danyv86/ME-1670---SOLIDWORKS-Functional-Design-Team-Project/Daniel Velazquez TOOLIO Drawings/BOLT DRAWING.PNG

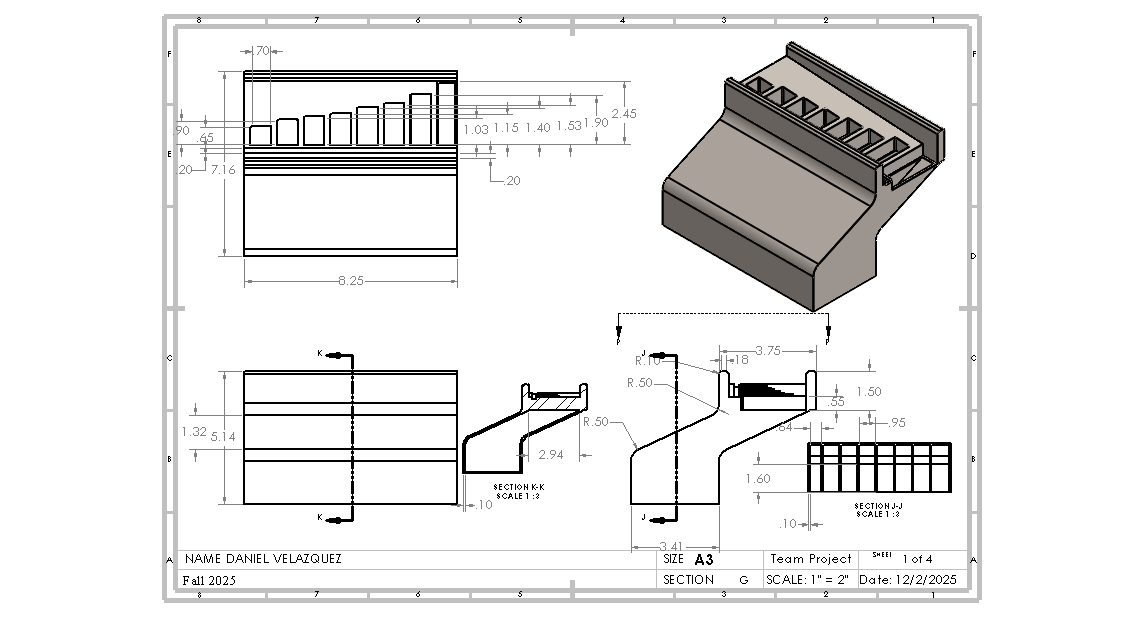
Daniel Velazquez TOOLIO Drawings/BOLT DRAWING.PNG
