danyv86/ME-1670---SOLIDWORKS-Functional-Design-Team-Project/Daniel Velazquez TOOLIO Drawings/REAL FINAL SUBASSEMLY DRAWINF.PNG

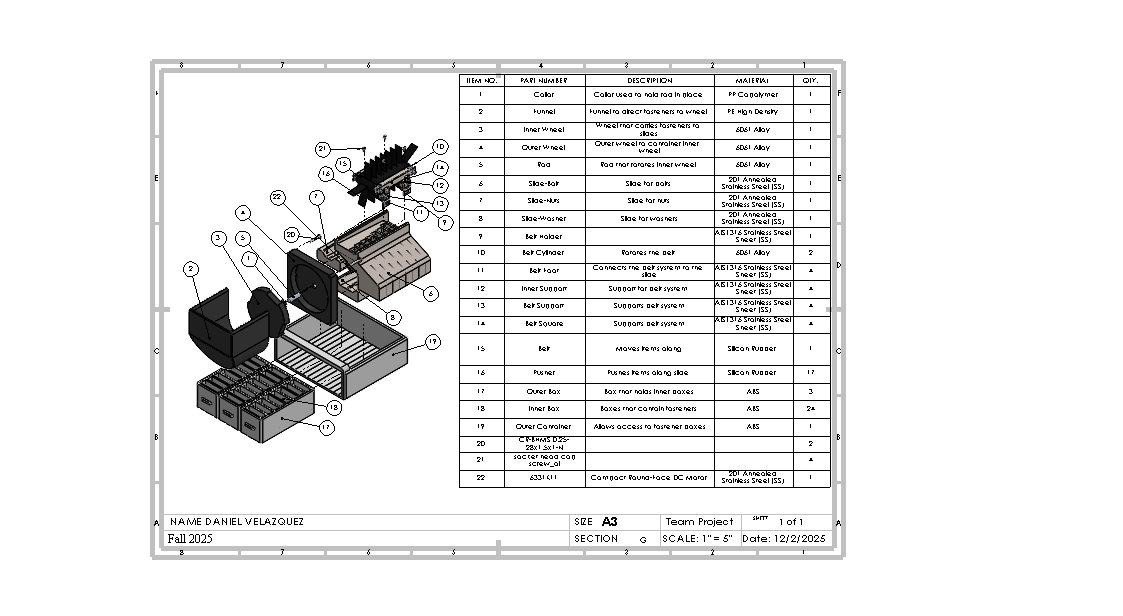
Daniel Velazquez TOOLIO Drawings/REAL FINAL SUBASSEMLY DRAWINF.PNG
