danyv86/ME-1670---SOLIDWORKS-Functional-Design-Team-Project/Daniel Velazquez TOOLIO Part PNGs/11.PNG

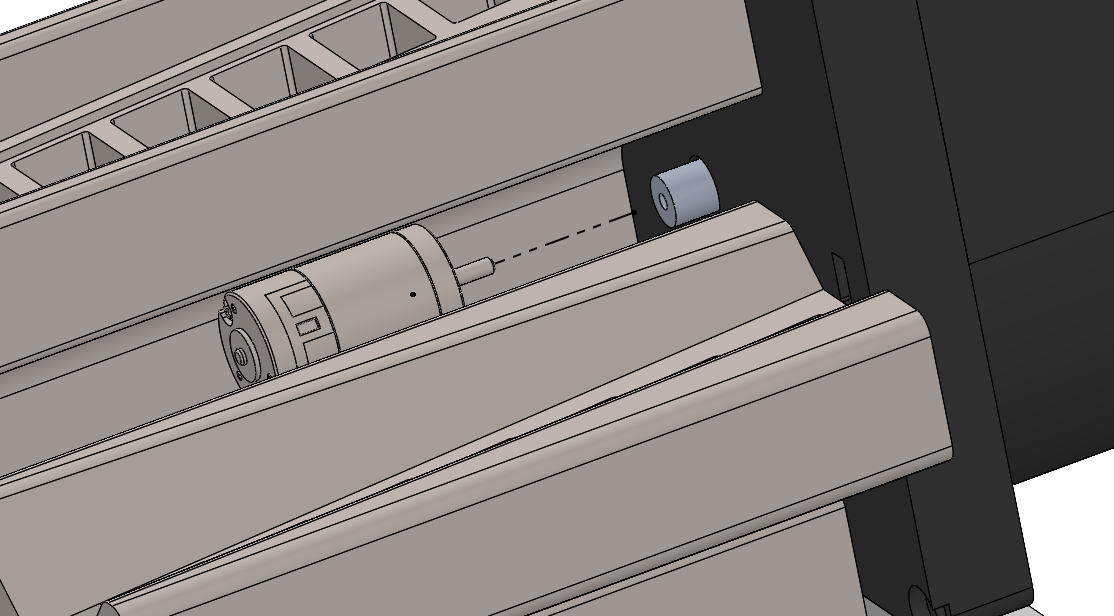
Daniel Velazquez TOOLIO Part PNGs/11.PNG
