danyv86/ME-1670---SOLIDWORKS-Functional-Design-Team-Project/Daniel Velazquez TOOLIO Part PNGs/al.PNG

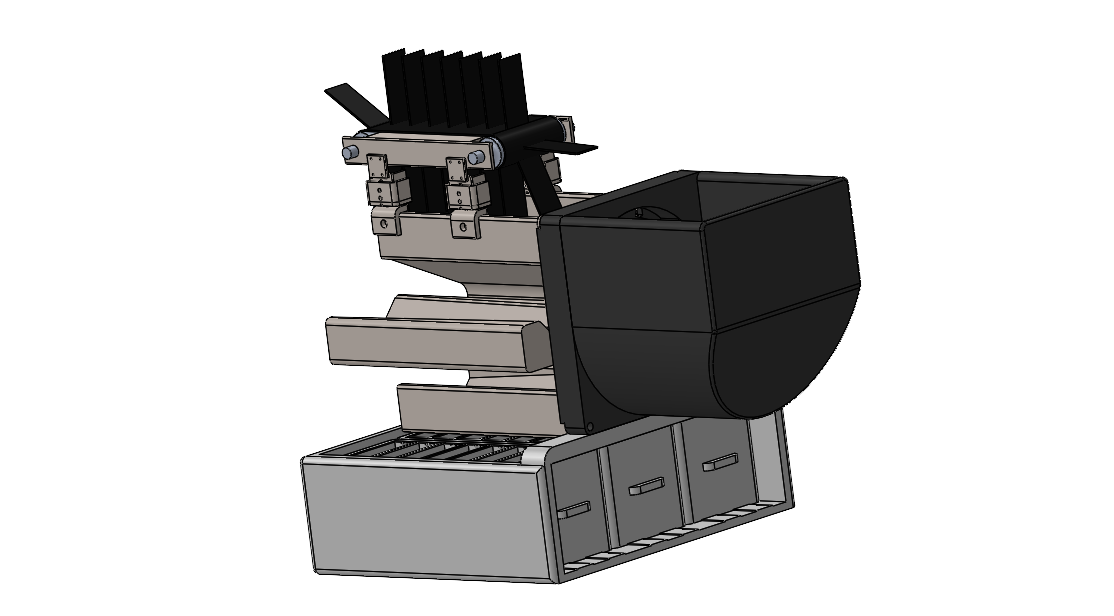
Daniel Velazquez TOOLIO Part PNGs/al.PNG
