danyv86/ME-1670---SOLIDWORKS-Functional-Design-Team-Project/Daniel Velazquez TOOLIO Part PNGs/Velazquez_Daniel_angle_bracket.PNG

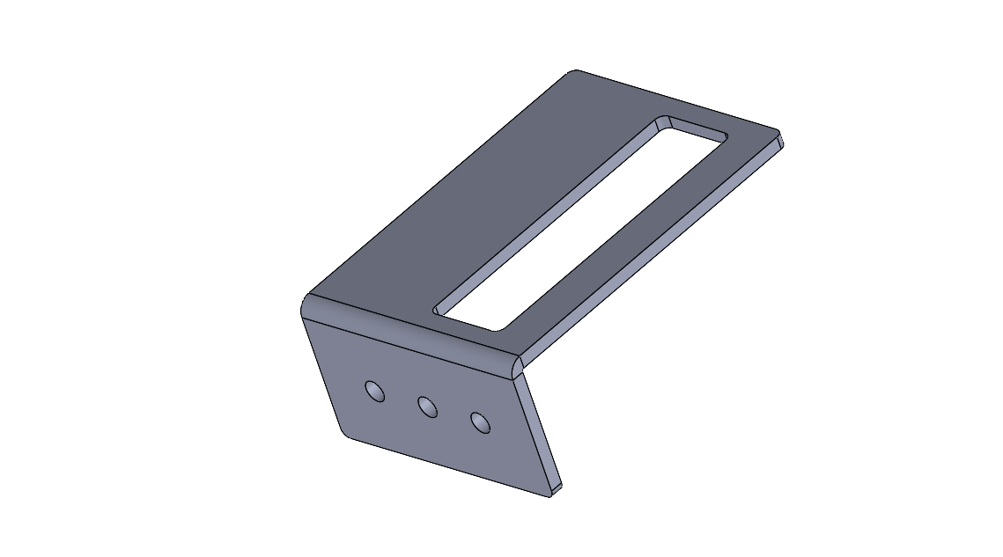
Daniel Velazquez TOOLIO Part PNGs/Velazquez_Daniel_angle_bracket.PNG
