danyv86/ME-1670---SOLIDWORKS-Functional-Design-Team-Project/Daniel Velazquez TOOLIO Part PNGs/Velazquez_Daniel_team_inner_wheel.PNG

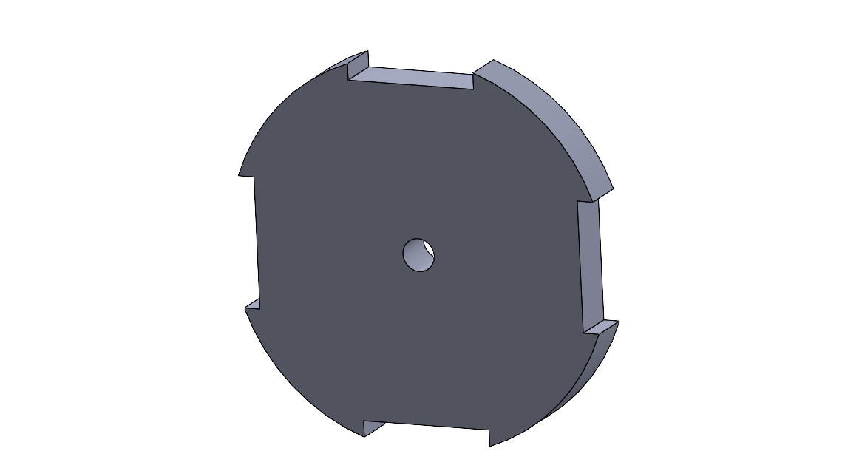
Daniel Velazquez TOOLIO Part PNGs/Velazquez_Daniel_team_inner_wheel.PNG
