danyv86/ME-1670---SOLIDWORKS-Functional-Design-Team-Project/Daniel Velazquez TOOLIO SLDPRTs/Velazquez_Daniel_team_outer_wheel.SLDPRT

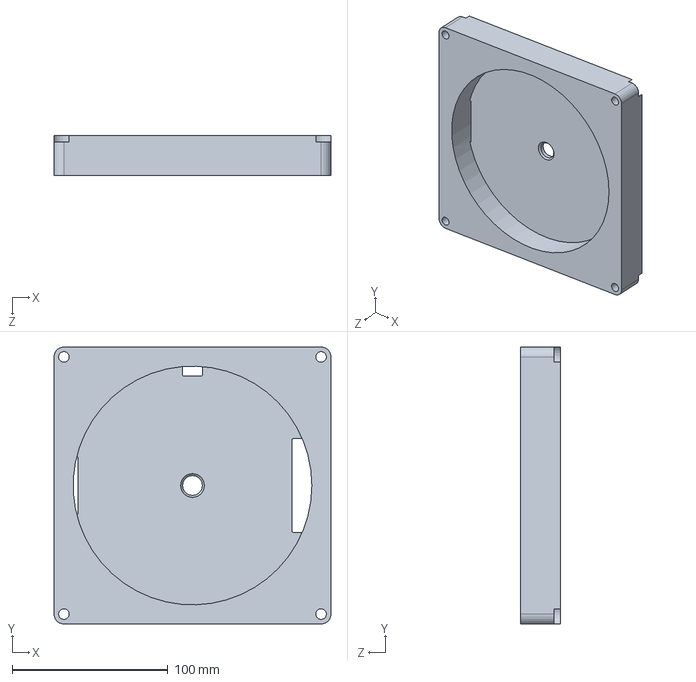
[picture p126: CAD file, 2026-04-10]
Daniel Velazquez TOOLIO SLDPRTs/Velazquez_Daniel_team_outer_wheel.SLDPRT
177.8 x 177.8 x 25.4 mm
