danyv86/ME-1670---SOLIDWORKS-Functional-Design-Team-Project/Daniel Velazquez TOOLIO SLDPRTs/Velazquez_Daniel_team_pusher.SLDPRT

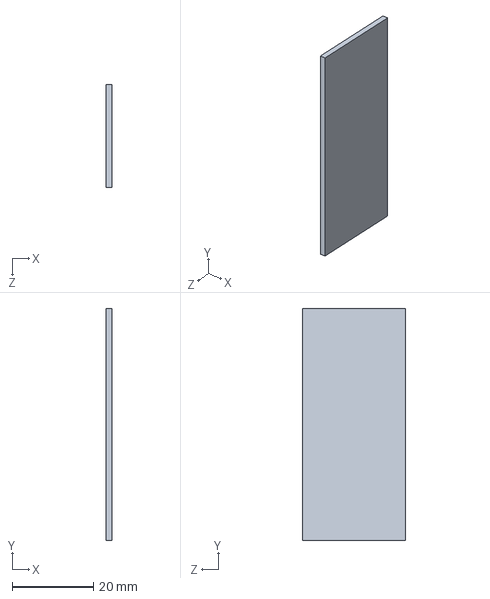
[picture p127: CAD file, 2026-04-10]
Daniel Velazquez TOOLIO SLDPRTs/Velazquez_Daniel_team_pusher.SLDPRT
1.52 x 57.1 x 25.4 mm
