danyv86/ME-1670---SOLIDWORKS-Functional-Design-Team-Project/Daniel Velazquez TOOLIO SLDPRTs/Velazquez_Daniel_team_funnel.SLDPRT

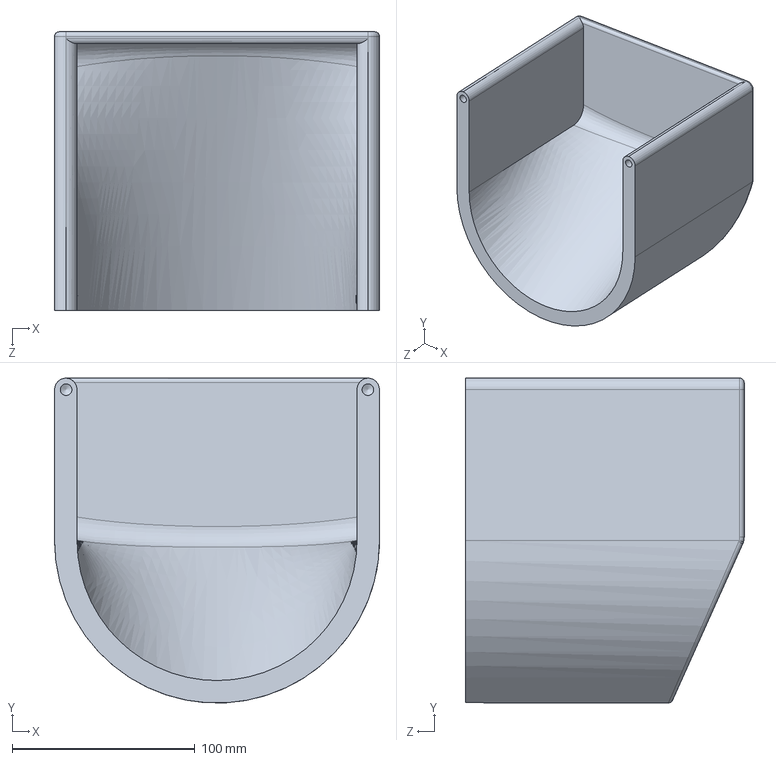
[picture p128: CAD file, 2026-04-10]
Daniel Velazquez TOOLIO SLDPRTs/Velazquez_Daniel_team_funnel.SLDPRT
177.8 x 177.7 x 152.4 mm
