danyv86/ME-1670---SOLIDWORKS-Functional-Design-Team-Project/Daniel Velazquez TOOLIO SLDPRTs/Velazquez_Daniel_team_slide_nut.SLDPRT

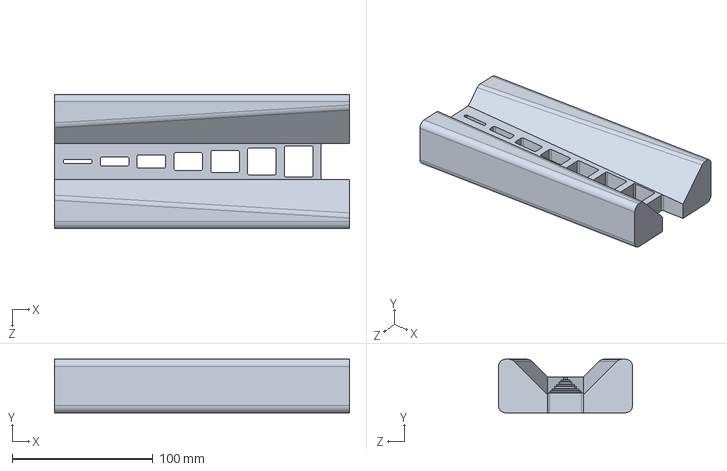
[picture p129: CAD file, 2026-04-10]
Daniel Velazquez TOOLIO SLDPRTs/Velazquez_Daniel_team_slide_nut.SLDPRT
209.6 x 38.1 x 95.2 mm
