danyv86/ME-1670---SOLIDWORKS-Functional-Design-Team-Project/Daniel Velazquez TOOLIO Part PNGs/Daniel_Velazquez_Subassembly.PNG

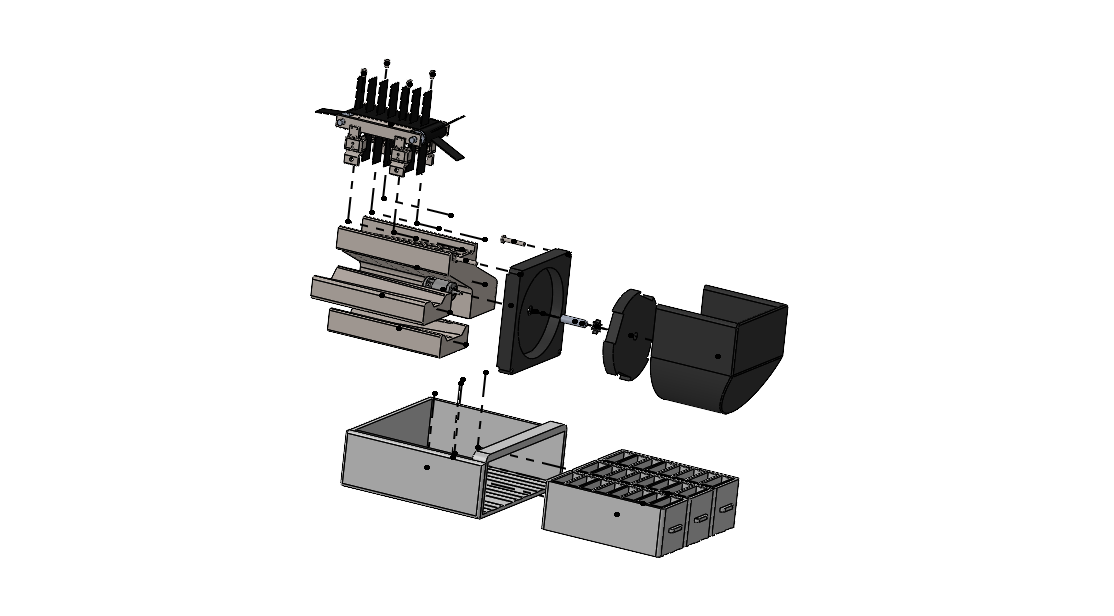
Daniel Velazquez TOOLIO Part PNGs/Daniel_Velazquez_Subassembly.PNG
